m-nenkov/TFM/Resultados/Pantalla/PID_prueba3.txt

DC0BA70AE00B9E0AE00B9E0AE30B930AE30B930AE40B980AE40B980AEE0BA10AFB0BB10AFB0BB10AFF0BC10AFF0BC10A040CC80A010CC90A010CC90A010CC90AFC0BB80AFC0BB80AFC0BB80A0B0CC40A0B0CC40A070CC70A110CD20A110CD20A110CD20A110CD20A110CD20A1F0C080B1F0C080B250C100B250C100B240C160B240C1B0B240C1B0B280C290B280C290B250C310B250C310B280C3C0B280C3C0B2A0C480B2A0C480B2D0C540B2D0C540B320C650B320C650B330C750B330C750B320C840B320C840B2D0C920B2D0C920B360CAB0B360CAB0B370CBB0B370CBB0B390CC70B390CC70B3D0CD60B3D0CD60B3D0CD60B300CDD0B300CDD0B2D0CE40B2D0CE40B2C0CF00B2C0CF00B270CF60B270CF60B1E0C000C1E0C000C200C0E0C200C0E0C1D0C190C1D0C190C1F0C280C1F0C280C220C2C0C220C2C0C1B0C340C1B0C340C190C390C190C390C120C390C120C390C120C3E0C120C3E0C0F0C3B0C0F0C3B0C010C3E0C010C3E0CFE0B460CFE0B460CF90B4A0CF90B4A0C080C630C080C630C0F0C740C0F0C740C0B0C790C0B0C790C090C820C090C820CF80B7F0CF80B7F0CF00B7A0CF00B7A0CF50B820CF50B820CF10B890CF10B890CED0B890CED0B890CF10B9B0CF10B9B0CDF0BA20CDF0BA20CDE0BAB0CDA0BBB0CDA0BBB0CD80BBE0CD80BBE0CE00BC90CE00BC90CD30BCF0CD30BCF0CD20BD70CD20BD70CCD0BDE0CCD0BDE0CC80BE40CC80BE40CCC0BED0CCC0BED0CC70BF60CC30BFF0CC30BFF0CC10B070DC10B070DBF0B110DBF0B110DBA0B170DBA0B170DB80B200DB80B200DB50B280DB50B280DB80B320DB70B390DB70B390DB60B410DB60B410DB40B460DB40B460DB00B4C0DB00B4C0DB30B570DAE0B5D0DAE0B5D0DAE0B660DAE0B660DAD0B6C0DAD0B6C0DA80B730DA80B730DAB0B7B0DA90B820DA90B820DA70B890DA70B890DA80B8F0DA80B8F0DA50B950DA50B950DA40B9A0DA30B9F0DA30B9F0DA20BA50DA20BA50DA20BA80DA20BA80DA00BAE0D9D0BB30D9D0BB30D950BB70D950BB70D8F0BBC0D8F0B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
F20EEB0DF20EEB0DF60EE10DF60EE10DF60ED50DF60ED50DF60ED50DF60EC80DF60EC80DF30EBC0DF30EBC0DF10EAF0DF10EAF0DEF0EA40DEF0EA40DEE0E9C0DEE0E9C0DEC0E910DE90E840D
